LonlyPan/FeixueMask/04_others/飞雪显示界面/表情设计.pdf

表情1（严肃）

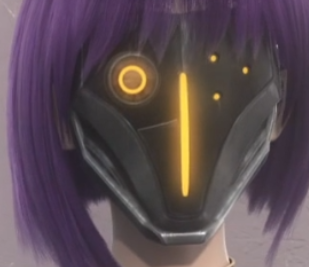
[picture p3: figure]

表情2（⽣⽓）

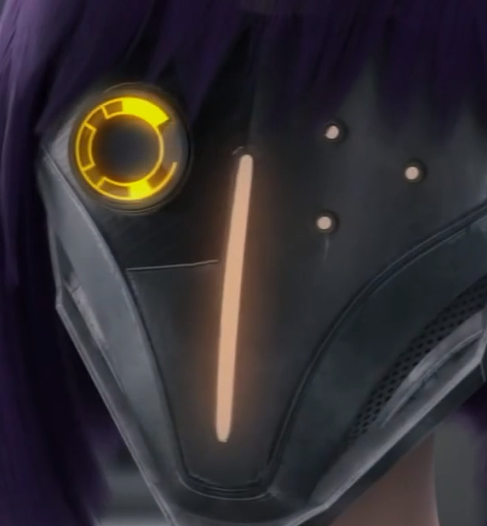
[picture p4: figure]

表情3（平常） 外圈⼀半亮度，内圈灰⾊

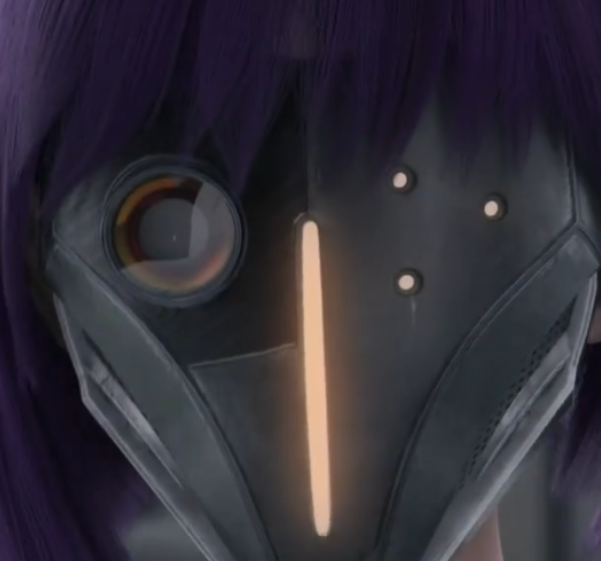
[picture p5: figure]

表情4 （看客）：中⼼圆满填充，⼀半亮度

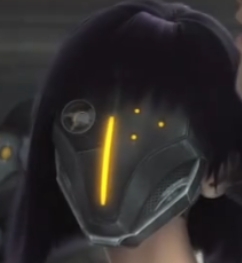
[picture p6: figure]
