LonlyPan/FeixueMask/02_Electronics/01_source/01_new_source/FeixueMask-V1.0/最终输出文件/LED_V1.0.pdf

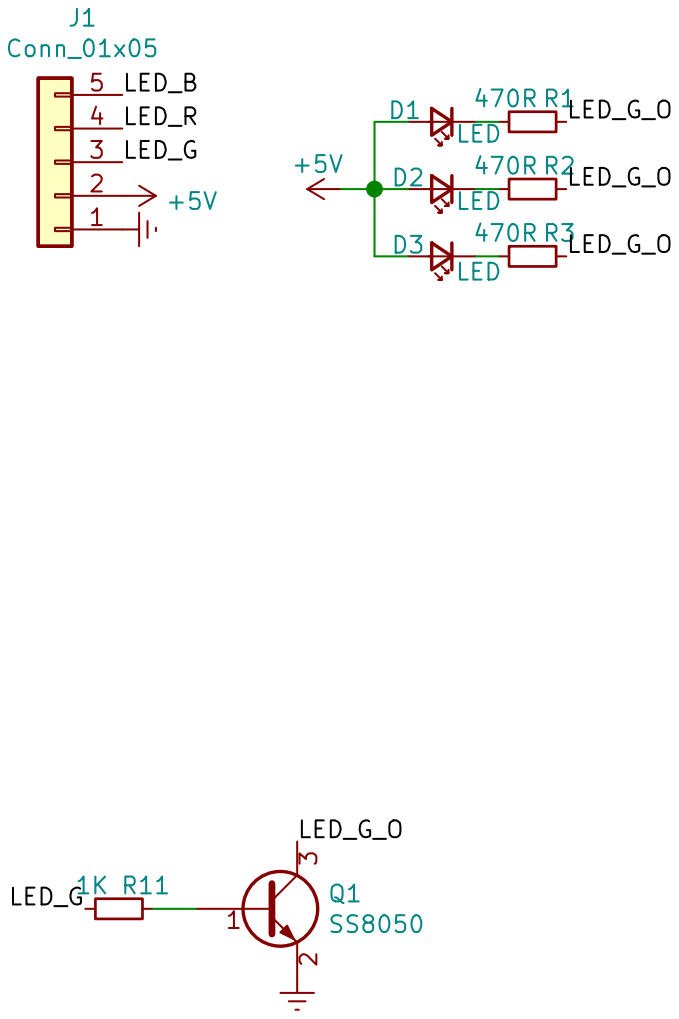
[picture p14: page 1]
