LonlyPan/FeixueMask/02_Electronics/01_source/01_new_source/FeixueMask-V1.0/最终输出文件/main_V1.0.pdf

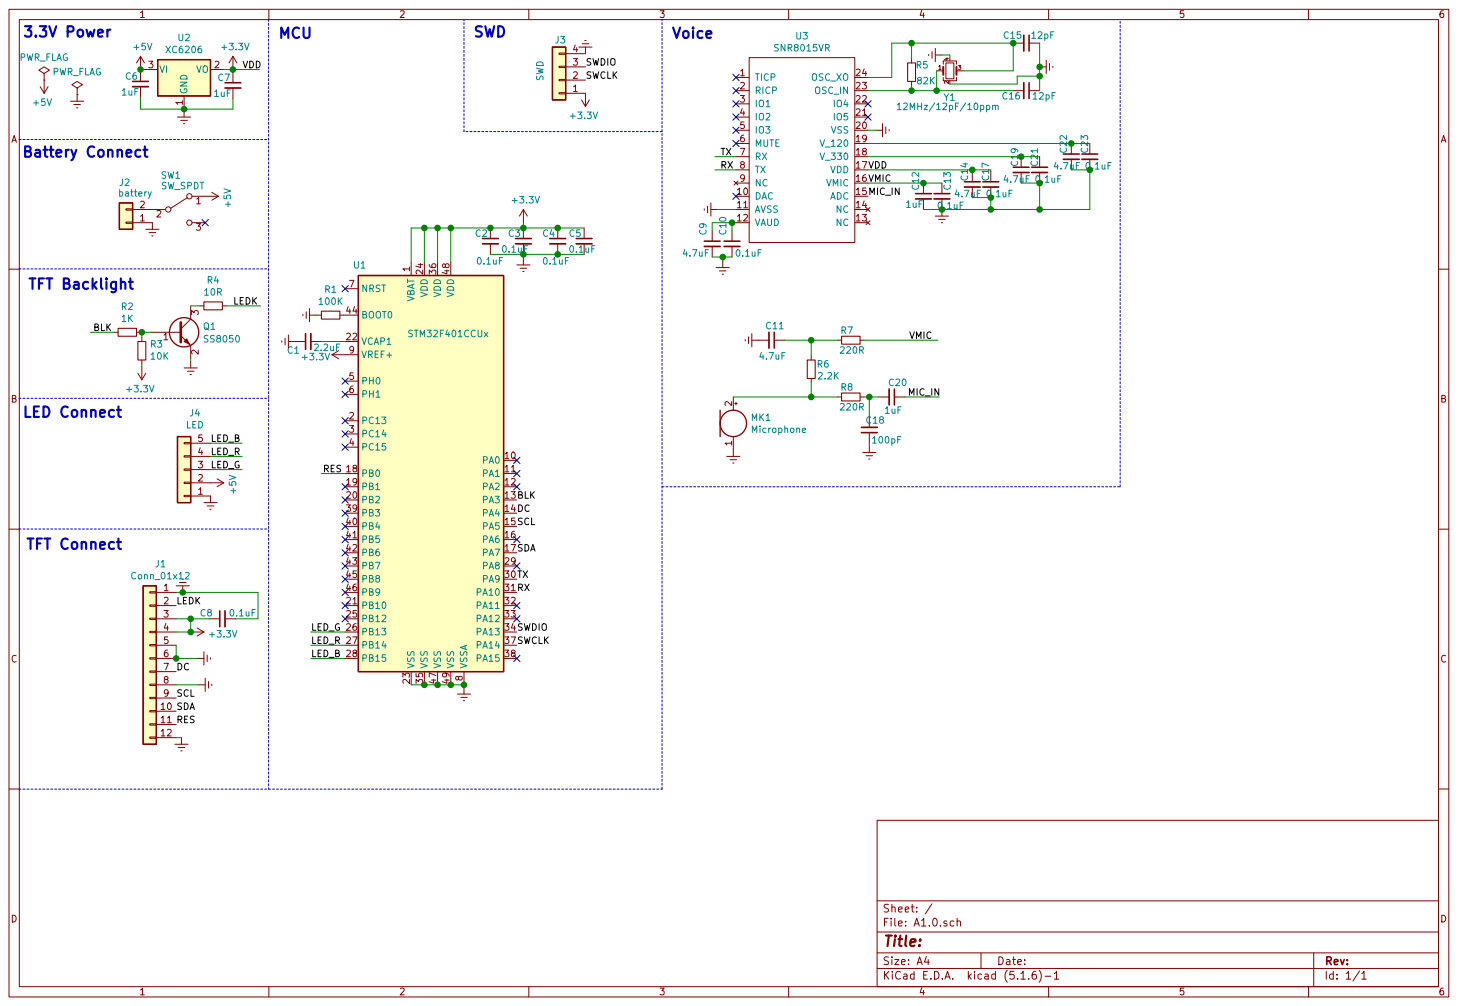
[picture p15: page 1]

1 VCAP1 22 VDD 24 VDD 36 VDD 48 VREF+ 9 VSS 23 VSS 35 VSS 47 VSS 49 VSSA
