LonlyPan/FeixueMask/02_Electronics/01_source/02_old_source/Test-A1.0/A1.0/A1.0.pdf

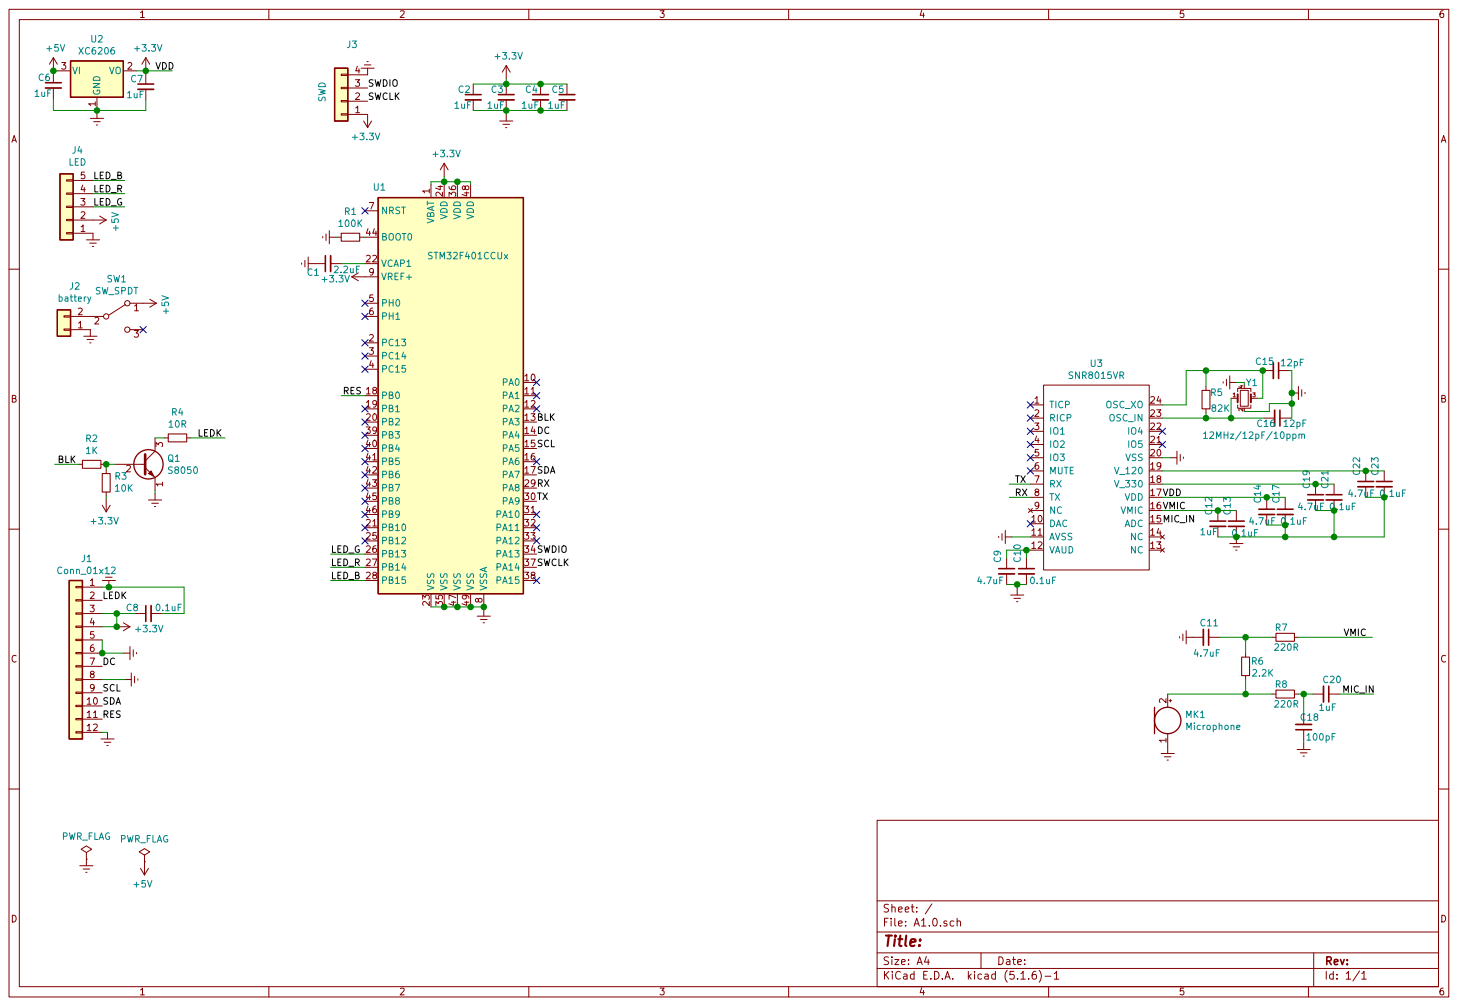
[picture p16: page 1]

VDD
VMIC

Id: 1/1 Title: File: A1.0.sch Sheet: / +3.3V
SCL RES DC
