LonlyPan/FeixueMask/01_Firmware/01_source/01_new_source/feixue-V1.0.0/User/lcd.h

/**
 * FeixueMask Firmware
 * Copyright (c) 2020 LonlyPan. All rights reserved.
 *
 *
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
 */

/**
  * @file:    lcd.h
  * @author:  LonlyPan
  * @version: V0.1
  * @date:    2020-12-10
  * @brief:   lcd底层驱动（初始话、发送命令等）
  *           lcd一些简单画图功能函数
  */
#ifndef LCD_H_
#define LCD_H_

#include "common.h"

#define USE_HORIZONTAL 2  //设置横屏或者竖屏显示 0或1为竖屏 2或3为横屏

#define LCD_W 240
#define LCD_H 240

//-----------------LCD端口定义----------------
#define LCD_RES_Clr()  HAL_GPIO_WritePin(RES_GPIO_Port, RES_Pin, GPIO_PIN_RESET)//RES
#define LCD_RES_Set()  HAL_GPIO_WritePin(RES_GPIO_Port, RES_Pin, GPIO_PIN_SET)

#define LCD_DC_Clr()   HAL_GPIO_WritePin(DC_GPIO_Port, DC_Pin, GPIO_PIN_RESET)//DC
#define LCD_DC_Set()   HAL_GPIO_WritePin(DC_GPIO_Port, DC_Pin, GPIO_PIN_SET)

#define LCD_CS_Clr()   //CS 实际硬件部分cs片选直接接地了
#define LCD_CS_Set()

#define LCD_BLK_Clr()  HAL_GPIO_WritePin(BLK_GPIO_Port, BLK_Pin, GPIO_PIN_RESET)//BLK
#define LCD_BLK_Set()  HAL_GPIO_WritePin(BLK_GPIO_Port, BLK_Pin, GPIO_PIN_SET)


void LCD_Writ_Bus(u8 data);// SPI写数据
void LCD_WR_DATA8(u8 data);// 写入一个字节
void LCD_WR_DATA(u16 data);// 写入两个字节
void LCD_WR_REG(u8 data);  // 写入一个指令
void LCD_Address_Set(u16 x1,u16 y1,u16 x2,u16 y2);//设置坐标函数
void lcd_init();// LCD初始化
void LCD_Fill(u16 xsta,u16 ysta,u16 xend,u16 yend,u16 color);
void LCD_DrawPoint(u16 x,u16 y,u16 color);//在指定位置画一个点
void DMA_LCD_Fill(u16 xsta,u16 ysta,u16 xend,u16 yend,u8 *color);
//画笔颜色
#define WHITE         	 0xFFFF
#define BLACK         	 0x0000
#define BLUE           	 0x001F
#define BRED             0XF81F
#define GRED 			 0XFFE0
#define GBLUE			 0X07FF
#define RED           	 0xF800
#define MAGENTA       	 0xF81F
#define GREEN         	 0x07E0
#define CYAN          	 0x7FFF
#define YELLOW        	 0xFFE0
#define BROWN 			 0XBC40 //棕色
#define BRRED 			 0XFC07 //棕红色
#define GRAY  			 0X8430 //灰色
#define DARKBLUE      	 0X01CF	//深蓝色
#define LIGHTBLUE      	 0X7D7C	//浅蓝色
#define GRAYBLUE       	 0X5458 //灰蓝色
#define LIGHTGREEN     	 0X841F //浅绿色
#define LGRAY 			 0XC618 //浅灰色(PANNEL),窗体背景色
#define LGRAYBLUE        0XA651 //浅灰蓝色(中间层颜色)
#define LBBLUE           0X2B12 //浅棕蓝色(选择条目的反色)

#endif /* LCD_H_ */
