LonlyPan/FeixueMask/01_Firmware/01_source/01_new_source/feixue-V1.0.0/GUI/lvgl_driver/lv_port_disp.c

/**
 * @file lv_port_disp.c
 *
 */

 /*Copy this file as "lv_port_disp.c" and set this value to "1" to enable content*/
#if 1

/*********************
 *      INCLUDES
 *********************/
#include "lv_port_disp.h"
#include "lcd.h"
#include "spi.h"
/*********************
 *      DEFINES
 *********************/

/**********************
 *      TYPEDEFS
 **********************/

/**********************
 *  STATIC PROTOTYPES
 **********************/
static void disp_init(void);

static void disp_flush(lv_disp_drv_t * disp_drv, const lv_area_t * area, lv_color_t * color_p);
#if LV_USE_GPU
static void gpu_blend(lv_color_t * dest, const lv_color_t * src, uint32_t length, lv_opa_t opa);
static void gpu_fill(lv_color_t * dest, uint32_t length, lv_color_t color);
#endif

/**********************
 *  STATIC VARIABLES
 **********************/
static lv_disp_drv_t * disp_p;
/**********************
 *      MACROS
 **********************/

/**********************
 *   GLOBAL FUNCTIONS
 **********************/

void lv_port_disp_init(void)
{
    /*-------------------------
     * Initialize your display
     * -----------------------*/
    disp_init();

    /*-----------------------------
     * Create a buffer for drawing
     *----------------------------*/
    /* Example for 1) */
    static lv_disp_buf_t disp_buf_1;
    static lv_color_t buf_1[LV_HOR_RES_MAX * 10];                      /*A buffer for 10 rows*/
	static lv_color_t buf_2[LV_HOR_RES_MAX * 10];
    lv_disp_buf_init(&disp_buf_1, buf_1, buf_2, LV_HOR_RES_MAX * 10);   /*Initialize the display buffer*/

    /*-----------------------------------
     * Register the display in LittlevGL
     *----------------------------------*/

    lv_disp_drv_t disp_drv;                         /*Descriptor of a display driver*/
    lv_disp_drv_init(&disp_drv);                    /*Basic initialization*/

    /*Set up the functions to access to your display*/

    /*Set the resolution of the display*/
		
    /*Used to copy the buffer's content to the display*/
    disp_drv.flush_cb = disp_flush;

    /*Set a display buffer*/
    disp_drv.buffer = &disp_buf_1;

#if LV_USE_GPU
    /*Optionally add functions to access the GPU. (Only in buffered mode, LV_VDB_SIZE != 0)*/

    /*Blend two color array using opacity*/
    disp_drv.gpu_blend = gpu_blend;

    /*Fill a memory array with a color*/
    disp_drv.gpu_fill = gpu_fill;
#endif

    /*Finally register the driver*/
    lv_disp_drv_register(&disp_drv);
}

/**********************
 *   STATIC FUNCTIONS
 **********************/

/* Initialize your display and the required peripherals. */
static void disp_init(void)
{
    /*You code here*/
}

/* Flush the content of the internal buffer the specific area on the display
 * You can use DMA or any hardware acceleration to do this operation in the background but
 * 'lv_disp_flush_ready()' has to be called when finished. */
static void disp_flush(lv_disp_drv_t * disp_drv, const lv_area_t * area, lv_color_t * color_p)
{
	  //uint16_t * color_array_16 = (uint16_t *) color_p;
	  //LCD_Fill(area->x1,area->y1,area->x2,area->y2,color_p->full);
	DMA_LCD_Fill(area->x1,area->y1,area->x2,area->y2,(u8*)color_p);
	disp_p = disp_drv;
	/*
	int32_t x, y;
    for(y = area->y1; y <= area->y2; y++) {
        for(x = area->x1; x <= area->x2; x++) {
            LCD_DrawPoint(x,y,color_p->full);
            color_p++;
       }
    }

	//*/
    /* IMPORTANT!!!
     * Inform the graphics library that you are ready with the flushing*/
    //lv_disp_flush_ready(disp_drv);
}
void HAL_SPI_TxCpltCallback(SPI_HandleTypeDef *hspi)
{
	HAL_SPI_DeInit(&hspi1);
	hspi1.Init.DataSize = SPI_DATASIZE_8BIT;
	HAL_SPI_Init(&hspi1);
	lv_disp_flush_ready(disp_p);
}
//void HAL_SPI_TxCpltCallback(SPI_HandleTypeDef *hspi)
//{
   // lv_disp_flush_ready(disp_p);
//}

/*OPTIONAL: GPU INTERFACE*/
#if LV_USE_GPU

/* If your MCU has hardware accelerator (GPU) then you can use it to blend to memories using opacity
 * It can be used only in buffered mode (LV_VDB_SIZE != 0 in lv_conf.h)*/
static void gpu_blend(lv_disp_drv_t * disp_drv, lv_color_t * dest, const lv_color_t * src, uint32_t length, lv_opa_t opa)
{
    /*It's an example code which should be done by your GPU*/
    uint32_t i;
    for(i = 0; i < length; i++) {
        dest[i] = lv_color_mix(dest[i], src[i], opa);
    }
}

/* If your MCU has hardware accelerator (GPU) then you can use it to fill a memory with a color
 * It can be used only in buffered mode (LV_VDB_SIZE != 0 in lv_conf.h)*/
static void gpu_fill_cb(lv_disp_drv_t * disp_drv, lv_color_t * dest_buf, lv_coord_t dest_width,
                    const lv_area_t * fill_area, lv_color_t color);
{
    /*It's an example code which should be done by your GPU*/
    uint32_t x, y;
    dest_buf += dest_width * fill_area->y1; /*Go to the first line*/

    for(y = fill_area->y1; y < fill_area->y2; y++) {
        for(x = fill_area->x1; x < fill_area->x2; x++) {
            dest_buf[x] = color;
        }
        dest_buf+=dest_width;    /*Go to the next line*/
    }
}

#endif  /*LV_USE_GPU*/

#else /* Enable this file at the top */

/* This dummy typedef exists purely to silence -Wpedantic. */
typedef int keep_pedantic_happy;
#endif
